Lonelybarbarian0/stm32-line-follower/stm32 line follower/line_follow_stm_BV.png

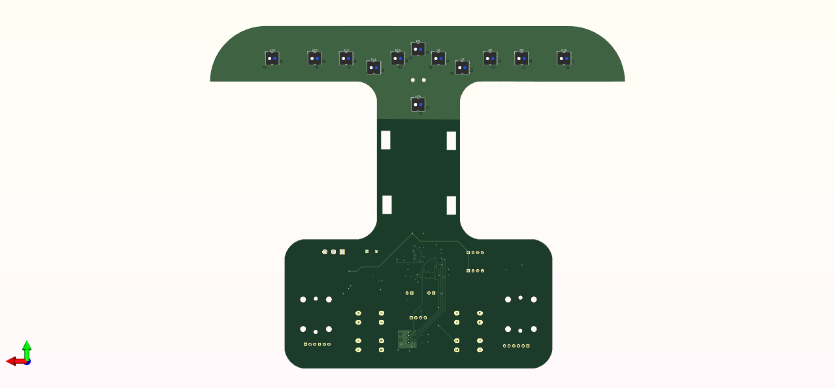
stm32 line follower/line_follow_stm_BV.png
